jbilander/ReAgnus-MegAChip/pics/hi-res/ReAgnus-MegAChip_pic4.png

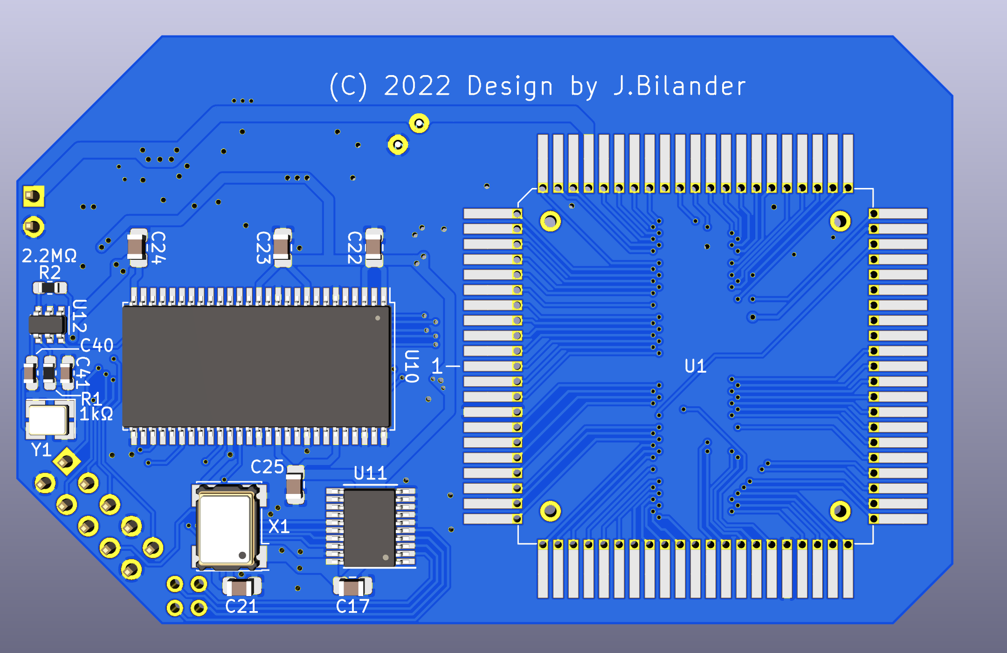
pics/hi-res/ReAgnus-MegAChip_pic4.png
