jbilander/ReAgnus-MegAChip/pics/ReAgnus-MegAChip_pic20.png

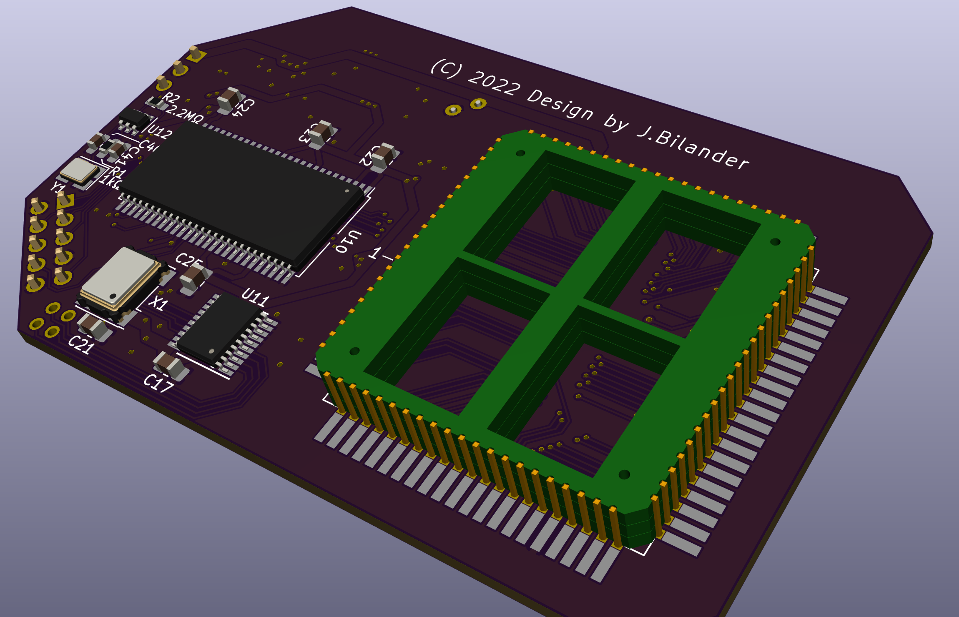
pics/ReAgnus-MegAChip_pic20.png
